sb43201/ACE-RFID-Handheld/images/05-handheld-back.jpg

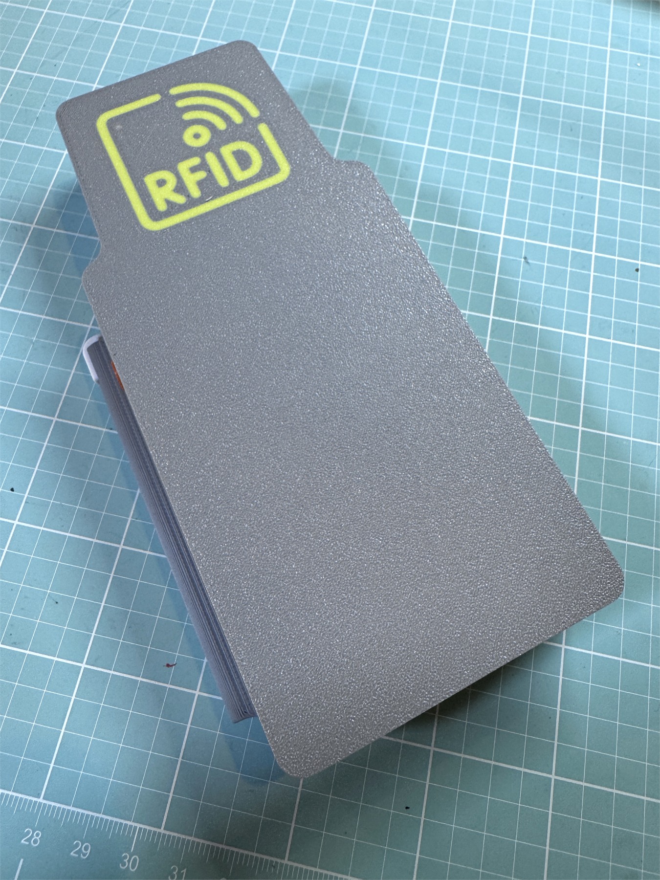
images/05-handheld-back.jpg
