sb43201/ACE-RFID-Handheld/images/06-ready-screen.jpg

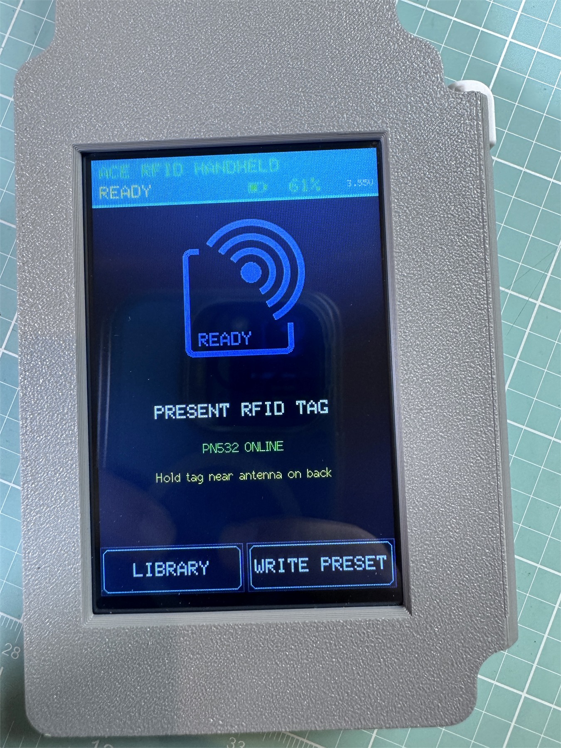
images/06-ready-screen.jpg
