sb43201/ACE-RFID-Handheld/images/08-write-preset-screen.jpg

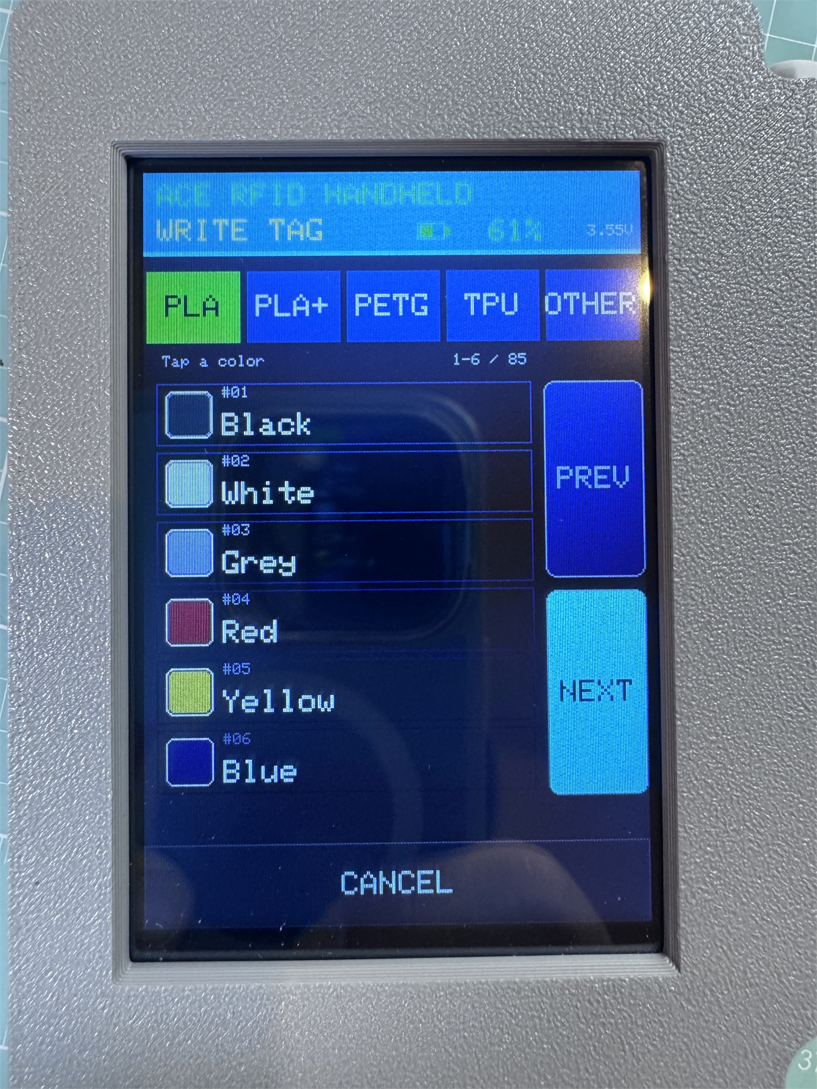
images/08-write-preset-screen.jpg
